abekjohnson17-ui/Ball-Launcher/src/STL Files/MAE476 PROJECT V2/ASSYV2.SLDASM

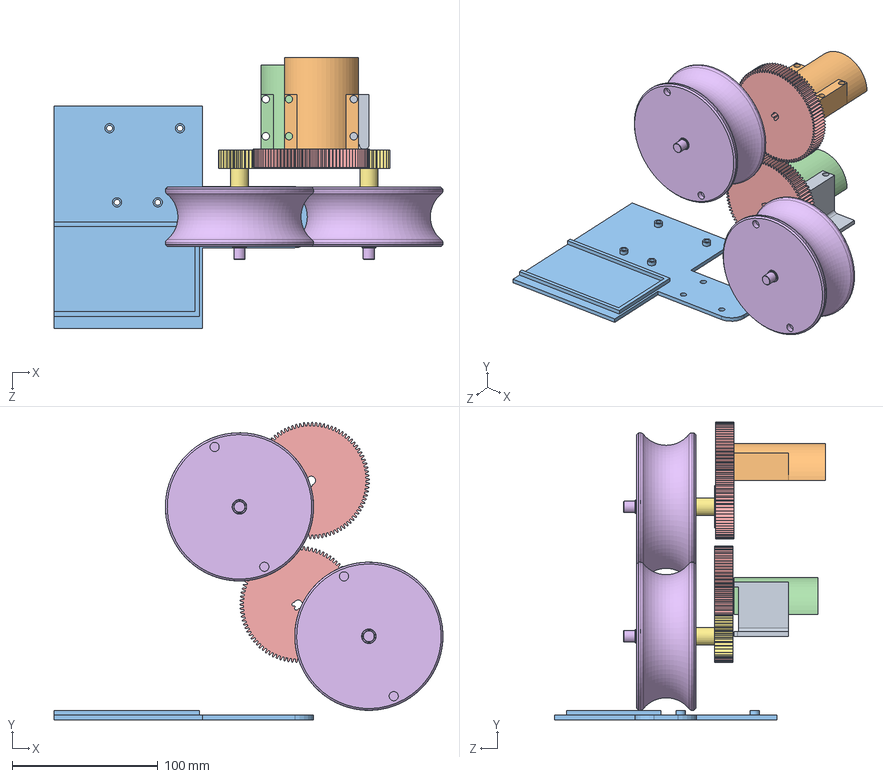
[picture p1: CAD file, 2025-12-07]
src/STL Files/MAE476 PROJECT V2/ASSYV2.SLDASM
266.6 x 204.0 x 185.6 mm
SHAFT-V2 x 2
DRIVENWHEEL x 2
GEARBOTTOM x 2
12VMOUNT
ELECTRONICS
12VMOUNT2
GEARHOLDER
