abekjohnson17-ui/Ball-Launcher/src/STL Files/MAE476 PROJECT V2/ASSY.SLDASM

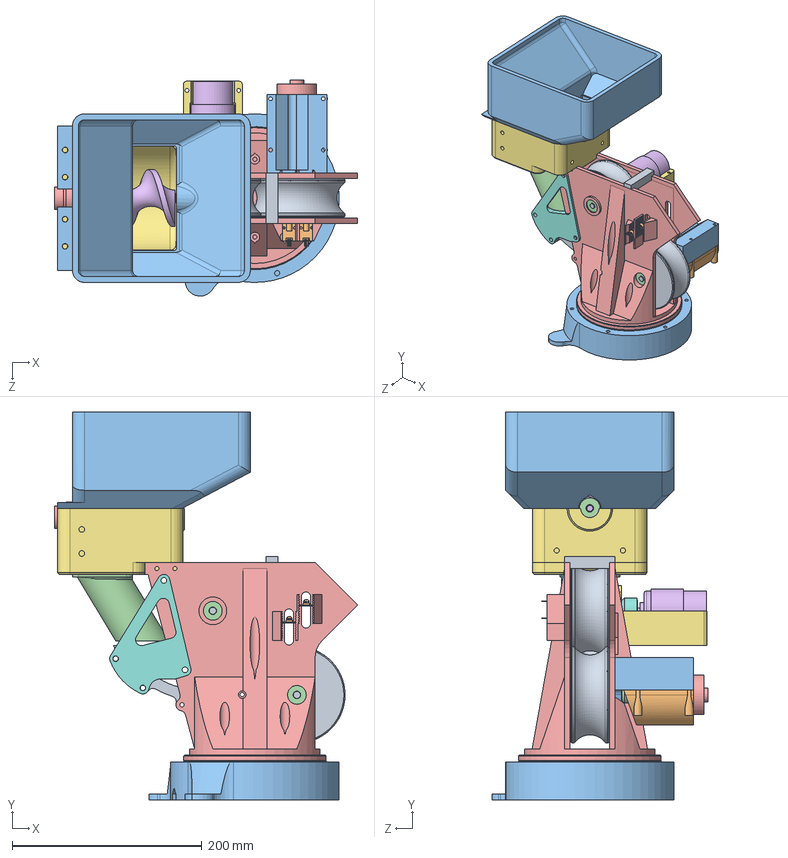
[picture p2: CAD file, 2025-12-07]
src/STL Files/MAE476 PROJECT V2/ASSY.SLDASM
319.9 x 409.2 x 228.0 mm
TESTTURRET
BEARING x 3
BASE
SERVO x 2
TRACK
TRACKARMS
AUGERTRAY
AUGER
MOTOR5V
CHUTE
BUCKET
LAZEREMITTER x 2
DRIVENWHEEL x 2
SHAFT
MOTORMOUNT2
MOTOR36V
MOTOR2
SHAFT2
MOTORMOUNT3
MOTORBRACKET3
SPREADER
