abekjohnson17-ui/Ball-Launcher/src/STL Files/MAE476 Project/MOTORMOUNT2.SLDPRT

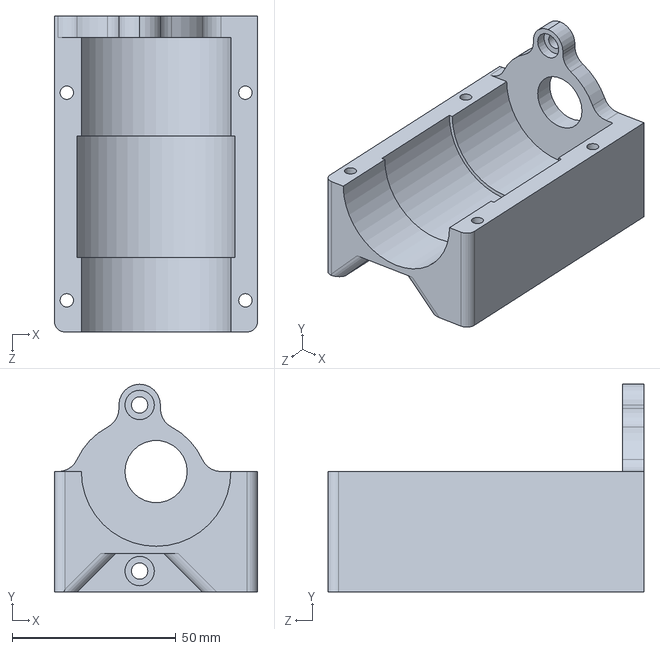
[picture p17: CAD file, 2025-12-07]
src/STL Files/MAE476 Project/MOTORMOUNT2.SLDPRT
62.1 x 63.5 x 96.6 mm
