abekjohnson17-ui/Ball-Launcher/src/STL Files/MAE476 PROJECT V2/TURRETBASE.SLDPRT

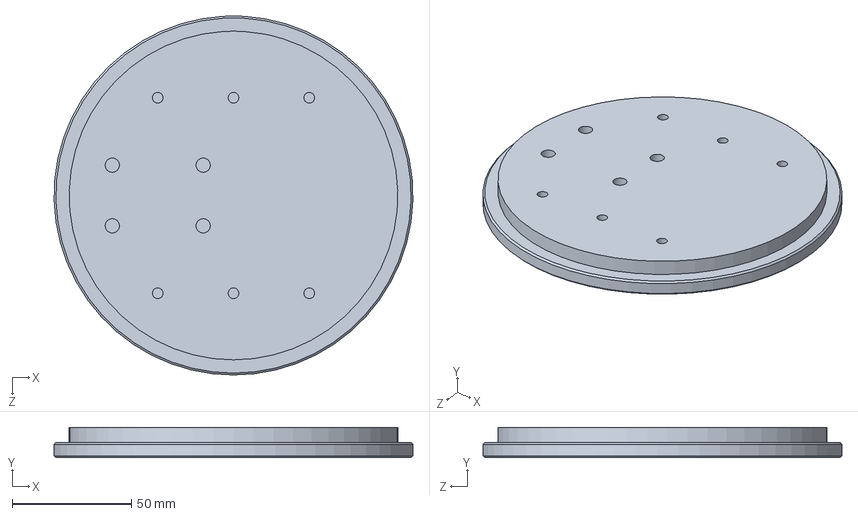
[picture p18: CAD file, 2025-12-07]
src/STL Files/MAE476 PROJECT V2/TURRETBASE.SLDPRT
150.4 x 12.7 x 150.5 mm
