abekjohnson17-ui/Ball-Launcher/src/STL Files/MAE476 Project/SHAFT.SLDPRT

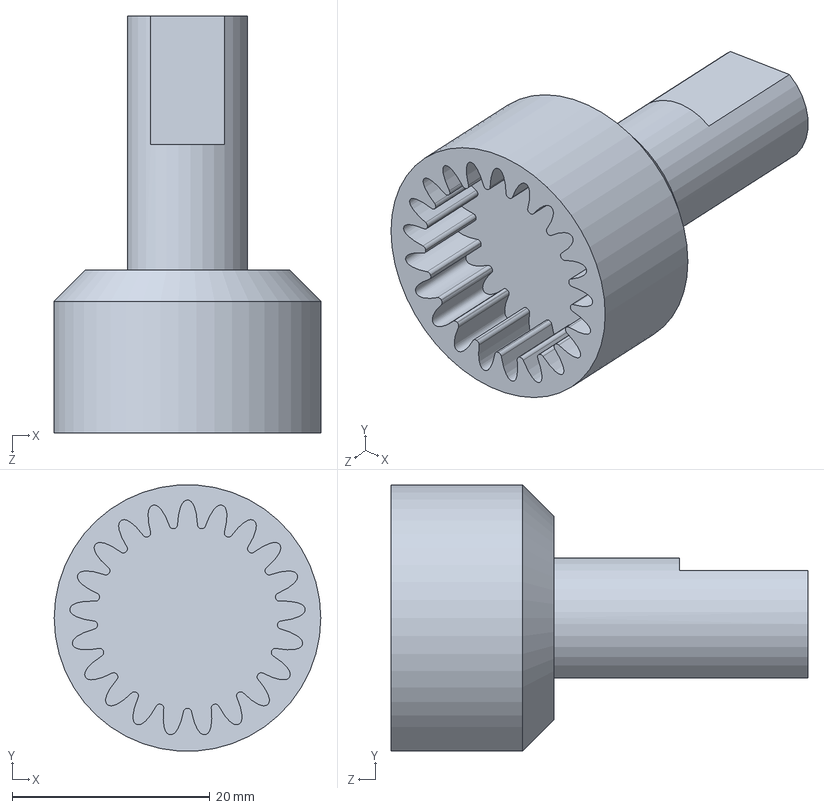
[picture p19: CAD file, 2025-12-07]
src/STL Files/MAE476 Project/SHAFT.SLDPRT
27.0 x 26.9 x 42.2 mm
