abekjohnson17-ui/Ball-Launcher/src/STL Files/MAE476 PROJECT V2/SPREADER.SLDPRT

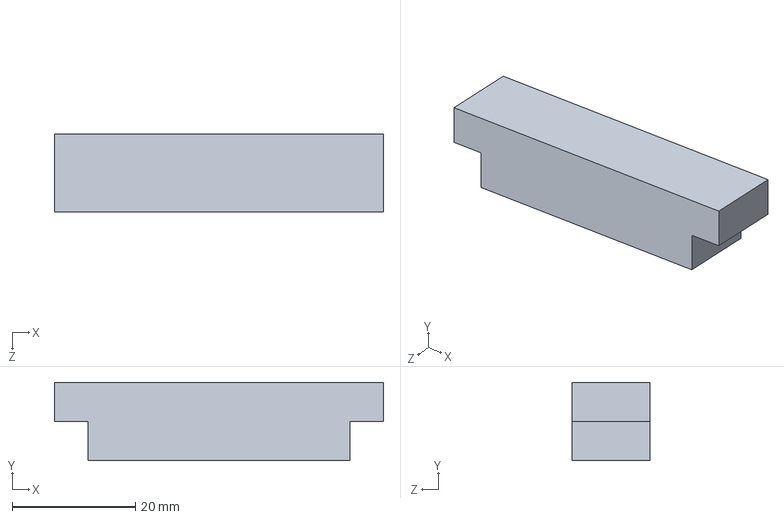
[picture p20: CAD file, 2025-12-07]
src/STL Files/MAE476 PROJECT V2/SPREADER.SLDPRT
53.4 x 12.7 x 12.7 mm
