abekjohnson17-ui/Ball-Launcher/src/STL Files/MAE476 PROJECT V2/SHAFT-V2.SLDPRT

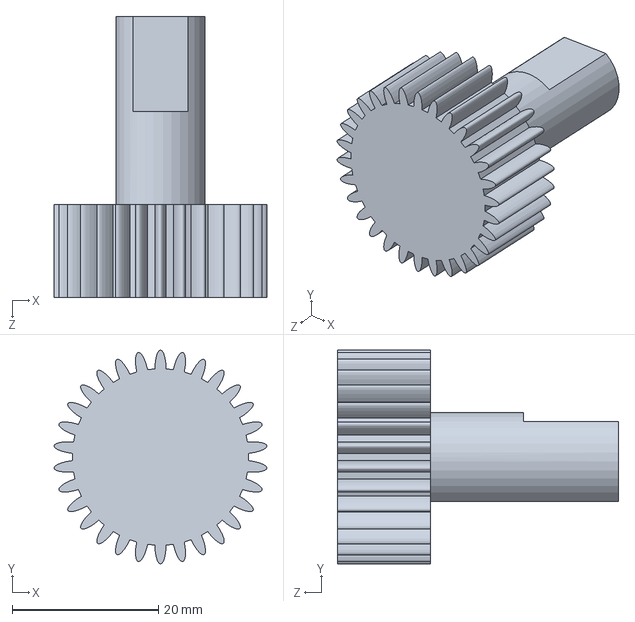
[picture p22: CAD file, 2025-12-07]
src/STL Files/MAE476 PROJECT V2/SHAFT-V2.SLDPRT
29.1 x 29.2 x 38.4 mm
