abekjohnson17-ui/Ball-Launcher/src/STL Files/MAE476 Project/MOTOR2.SLDPRT

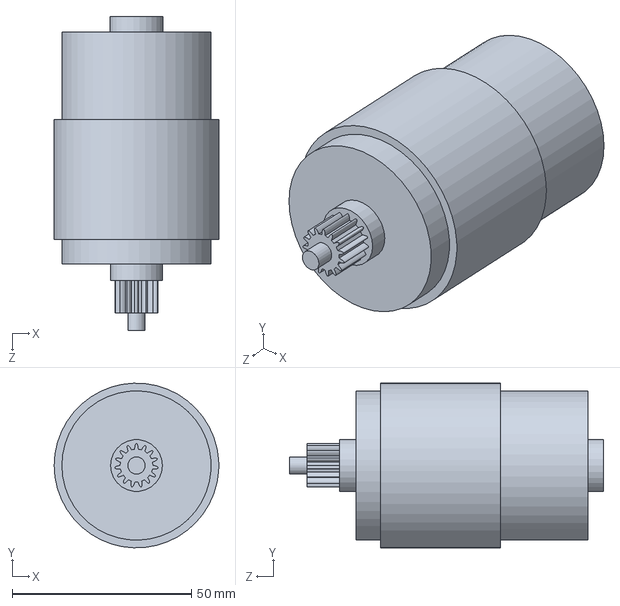
[picture p23: CAD file, 2025-12-07]
src/STL Files/MAE476 Project/MOTOR2.SLDPRT
46.0 x 45.9 x 87.6 mm
