abekjohnson17-ui/Ball-Launcher/src/STL Files/MAE476 Project/MOTORBRACKET3.SLDPRT

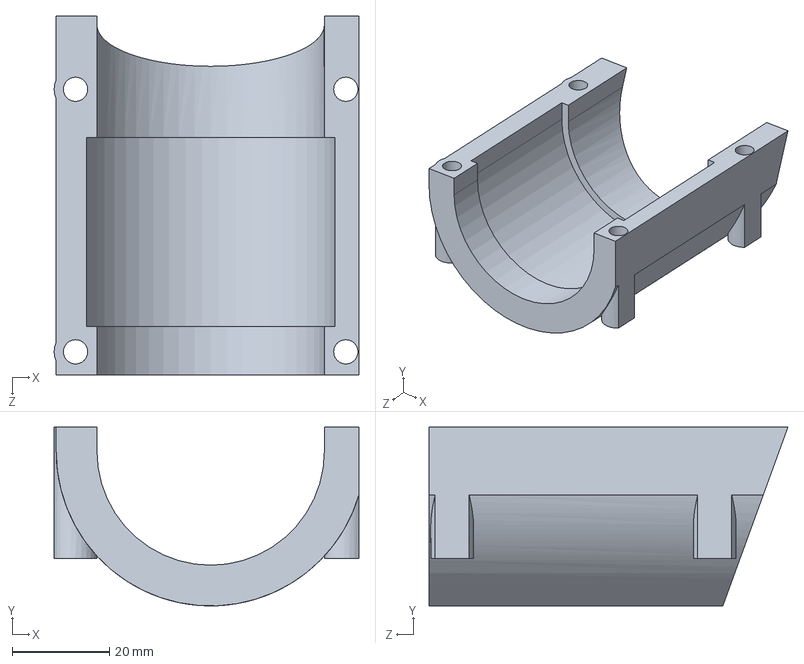
[picture p24: CAD file, 2025-12-07]
src/STL Files/MAE476 Project/MOTORBRACKET3.SLDPRT
62.7 x 36.8 x 73.8 mm
