abekjohnson17-ui/Ball-Launcher/src/STL Files/MAE476 Project/AUGERTRAY.SLDPRT

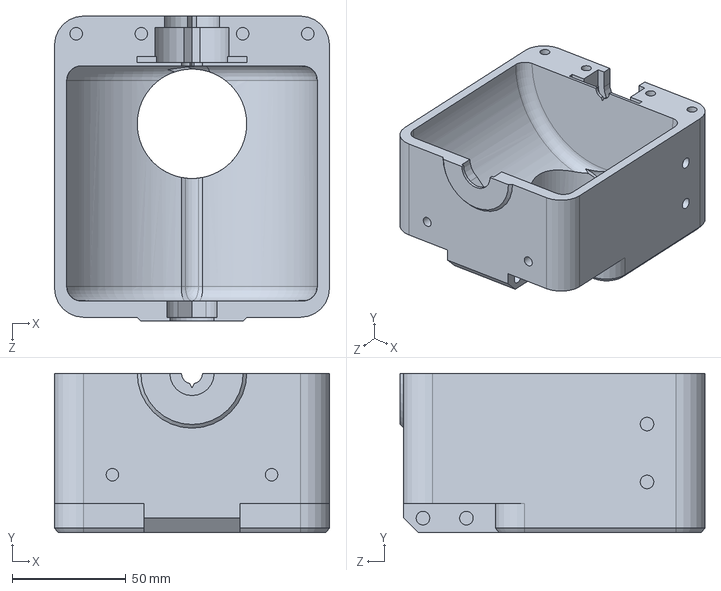
[picture p25: CAD file, 2025-12-07]
src/STL Files/MAE476 Project/AUGERTRAY.SLDPRT
120.7 x 69.8 x 133.7 mm
