abekjohnson17-ui/Ball-Launcher/src/STL Files/MAE476 Project/BUCKET.SLDPRT

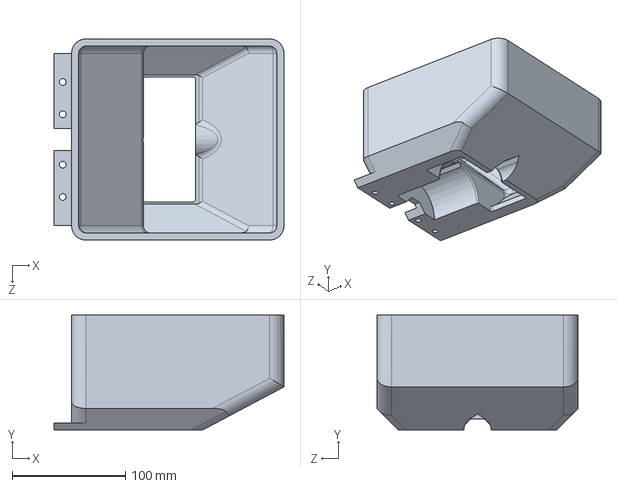
[picture p26: CAD file, 2025-12-07]
src/STL Files/MAE476 Project/BUCKET.SLDPRT
203.2 x 101.6 x 177.8 mm
