abekjohnson17-ui/Ball-Launcher/src/STL Files/MAE476 Project/AUGER.SLDPRT

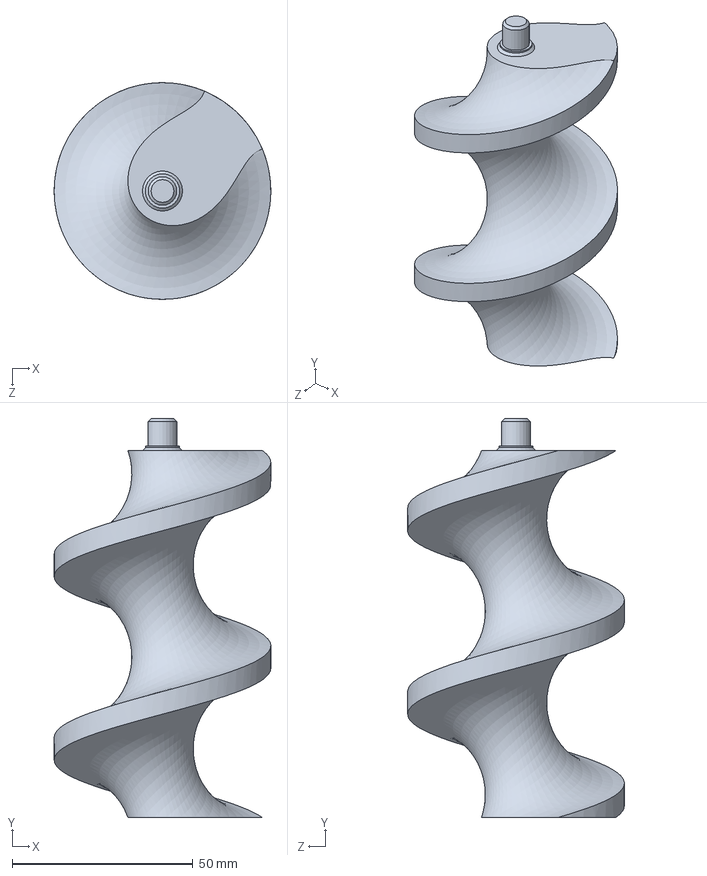
[picture p27: CAD file, 2025-12-07]
src/STL Files/MAE476 Project/AUGER.SLDPRT
60.0 x 110.5 x 60.0 mm
