abekjohnson17-ui/Ball-Launcher/src/STL Files/MAE476 Project/BEARING.SLDPRT

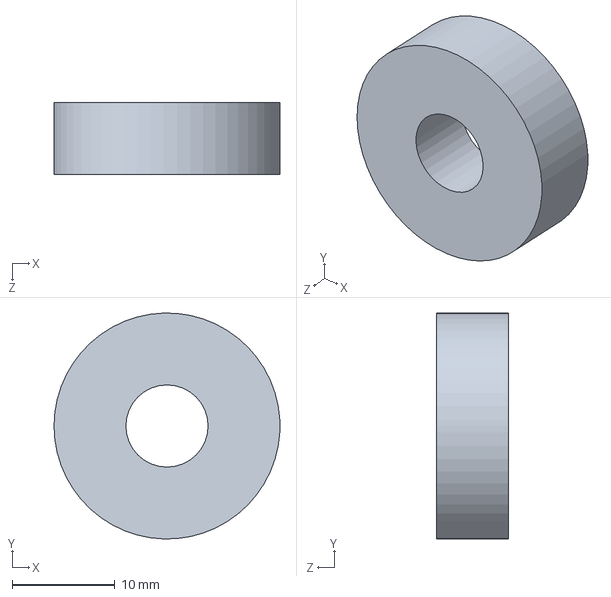
[picture p28: CAD file, 2025-12-07]
src/STL Files/MAE476 Project/BEARING.SLDPRT
22.0 x 22.0 x 7.00 mm
