abekjohnson17-ui/Ball-Launcher/src/STL Files/MAE476 PROJECT V2/MOTOR36V.SLDPRT

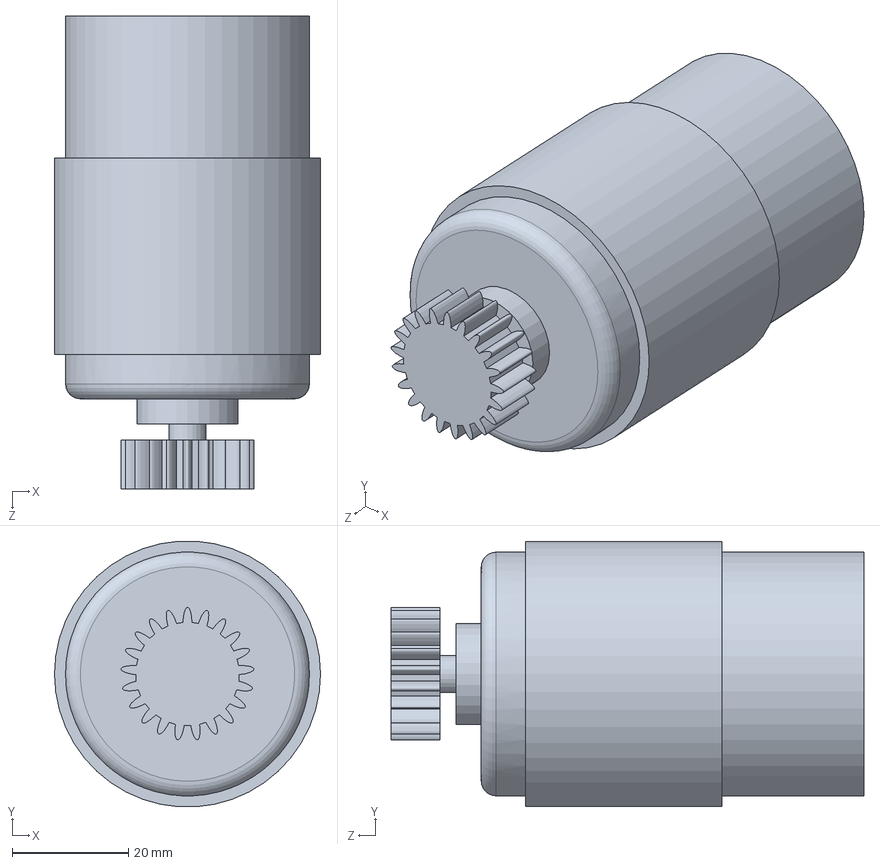
[picture p29: CAD file, 2025-12-07]
src/STL Files/MAE476 PROJECT V2/MOTOR36V.SLDPRT
45.7 x 45.6 x 81.3 mm
