abekjohnson17-ui/Ball-Launcher/src/STL Files/MAE476 Project/SHAFT2.SLDPRT

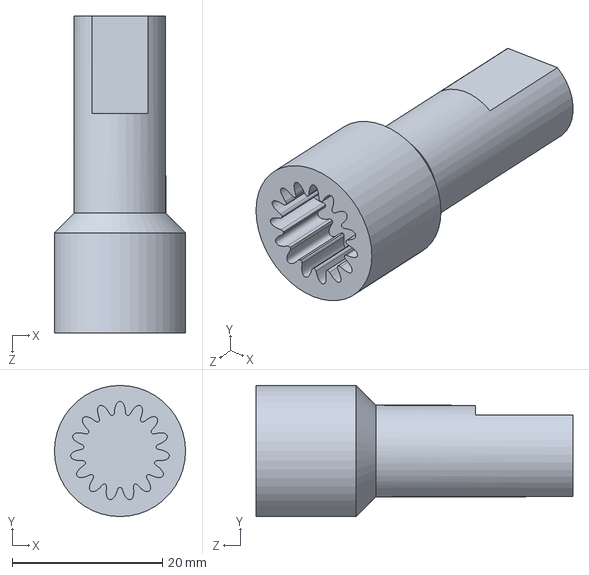
[picture p30: CAD file, 2025-12-07]
src/STL Files/MAE476 Project/SHAFT2.SLDPRT
17.5 x 17.5 x 42.2 mm
