abekjohnson17-ui/Ball-Launcher/src/STL Files/MAE476 PROJECT V2/MOTOR5V.SLDPRT

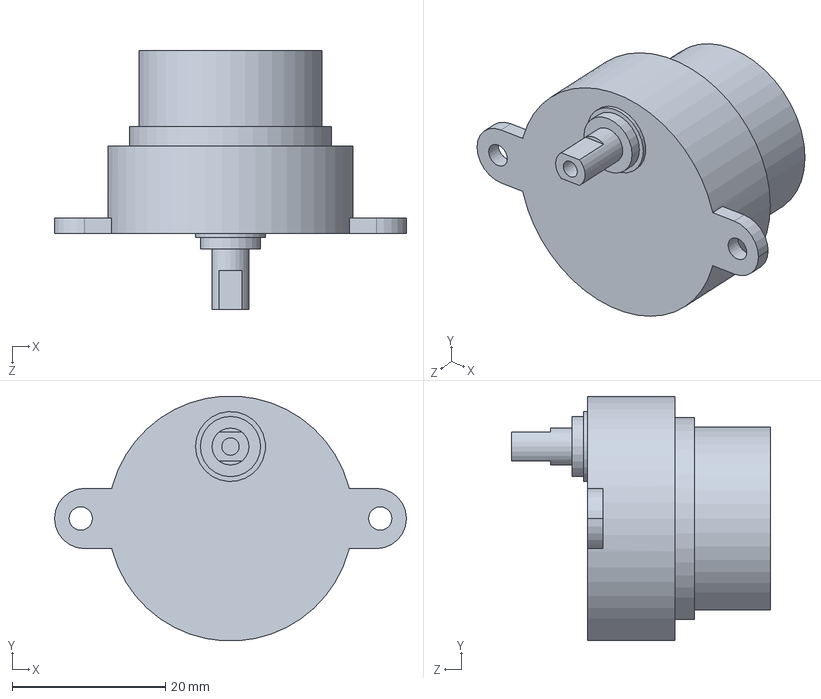
[picture p31: CAD file, 2025-12-07]
src/STL Files/MAE476 PROJECT V2/MOTOR5V.SLDPRT
46.0 x 31.9 x 33.8 mm
