abekjohnson17-ui/Ball-Launcher/src/STL Files/MAE476 Project/TRACK.SLDPRT

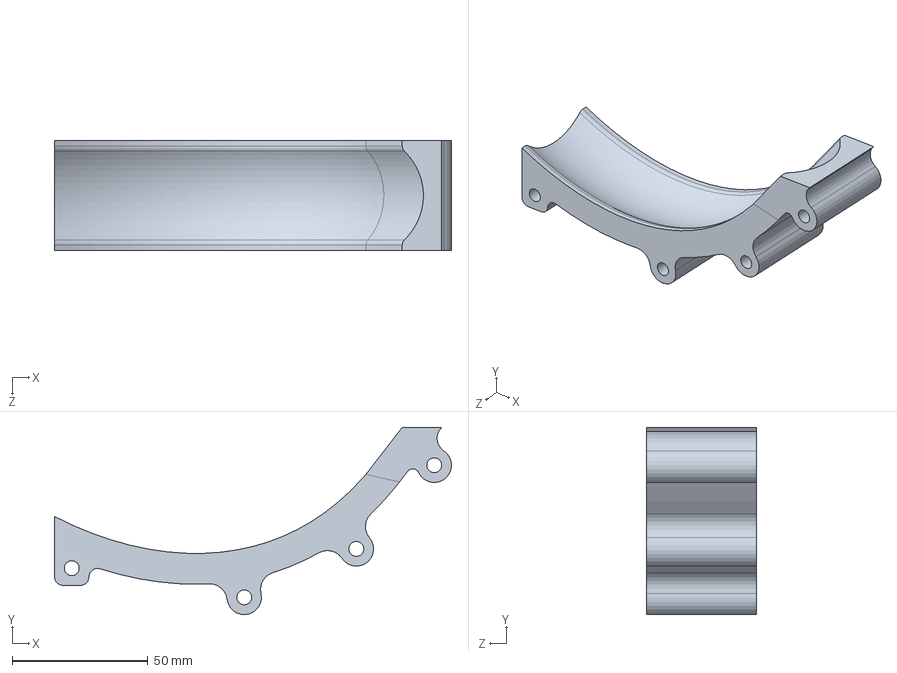
[picture p32: CAD file, 2025-12-07]
src/STL Files/MAE476 Project/TRACK.SLDPRT
146.1 x 68.9 x 40.6 mm
