abekjohnson17-ui/Ball-Launcher/src/STL Files/MAE476 Project/MOTORMOUNT.SLDPRT

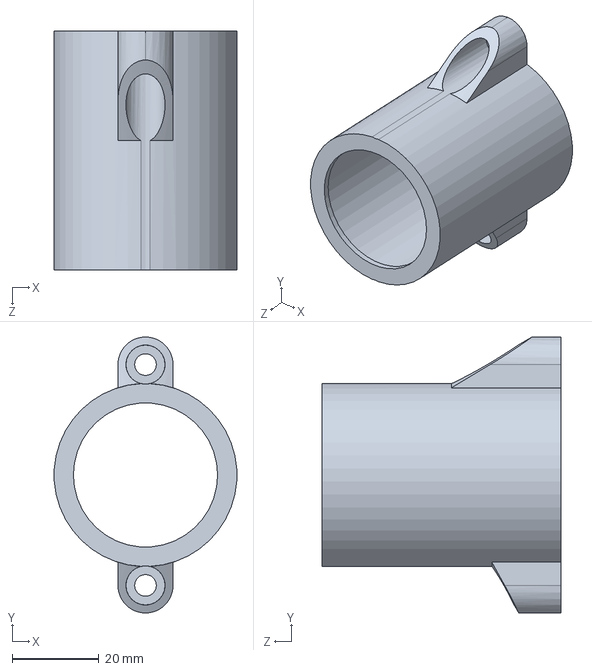
[picture p33: CAD file, 2025-12-07]
src/STL Files/MAE476 Project/MOTORMOUNT.SLDPRT
42.0 x 63.5 x 54.9 mm
