abekjohnson17-ui/Ball-Launcher/src/STL Files/MAE476 Project/TURRETLEFT.SLDPRT

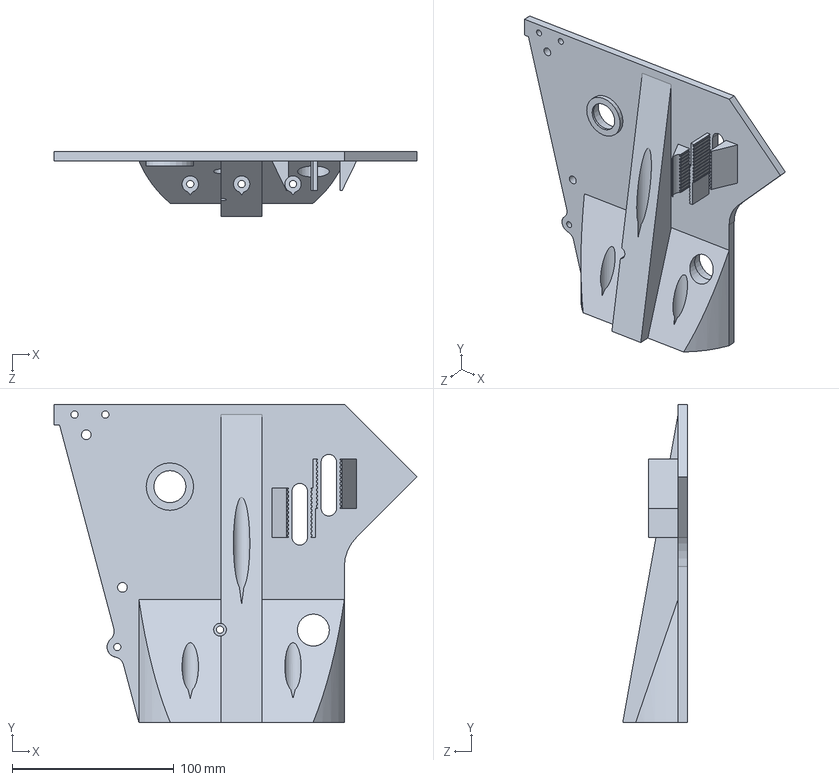
[picture p34: CAD file, 2025-12-07]
src/STL Files/MAE476 Project/TURRETLEFT.SLDPRT
224.4 x 196.9 x 40.0 mm
