abekjohnson17-ui/Ball-Launcher/src/STL Files/MAE476 Project/MOTOR12V.SLDPRT

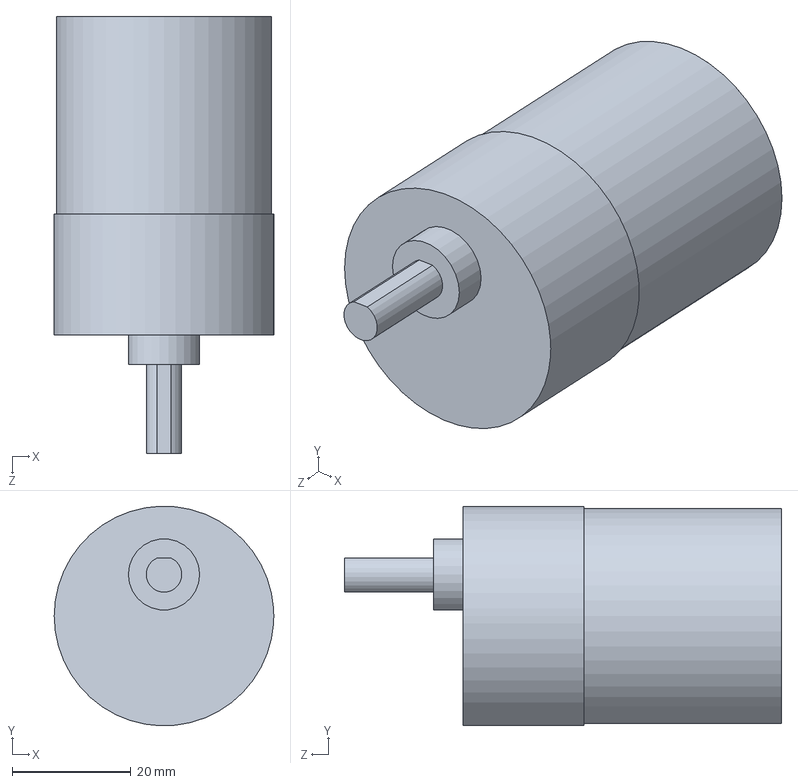
[picture p35: CAD file, 2025-12-07]
src/STL Files/MAE476 Project/MOTOR12V.SLDPRT
37.0 x 37.0 x 73.6 mm
