abekjohnson17-ui/Ball-Launcher/src/STL Files/MAE476 PROJECT V2/MOTORMOUTBOT.SLDPRT

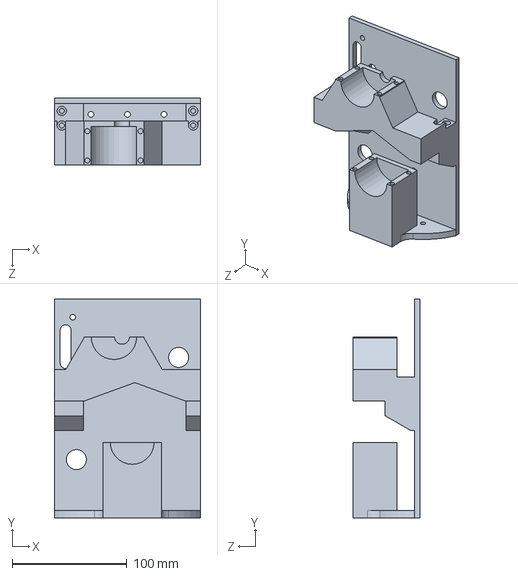
[picture p36: CAD file, 2025-12-07]
src/STL Files/MAE476 PROJECT V2/MOTORMOUTBOT.SLDPRT
127.0 x 190.5 x 58.1 mm
