abekjohnson17-ui/Ball-Launcher/src/STL Files/MAE476 PROJECT V2/shim.SLDPRT

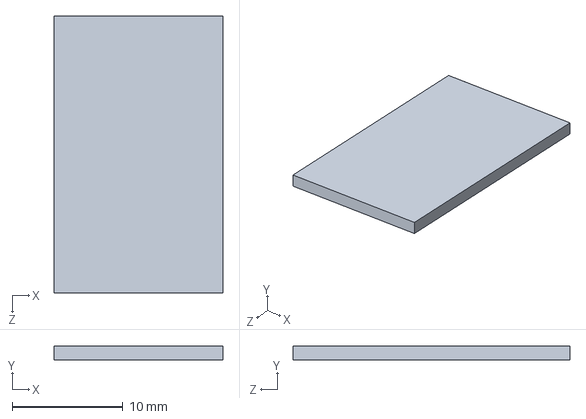
[picture p37: CAD file, 2025-12-07]
src/STL Files/MAE476 PROJECT V2/shim.SLDPRT
15.2 x 1.27 x 25.0 mm
