abekjohnson17-ui/Ball-Launcher/src/STL Files/MAE476 Project/BASETOP.SLDPRT

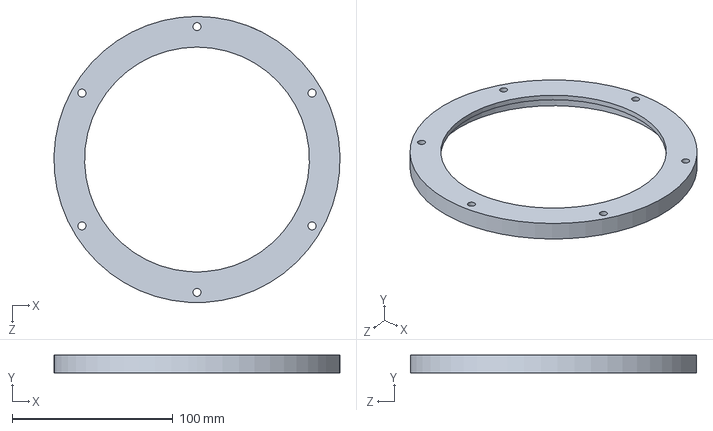
[picture p38: CAD file, 2025-12-07]
src/STL Files/MAE476 Project/BASETOP.SLDPRT
177.7 x 11.1 x 177.8 mm
