abekjohnson17-ui/Ball-Launcher/src/STL Files/MAE476 Project/BALL.SLDPRT

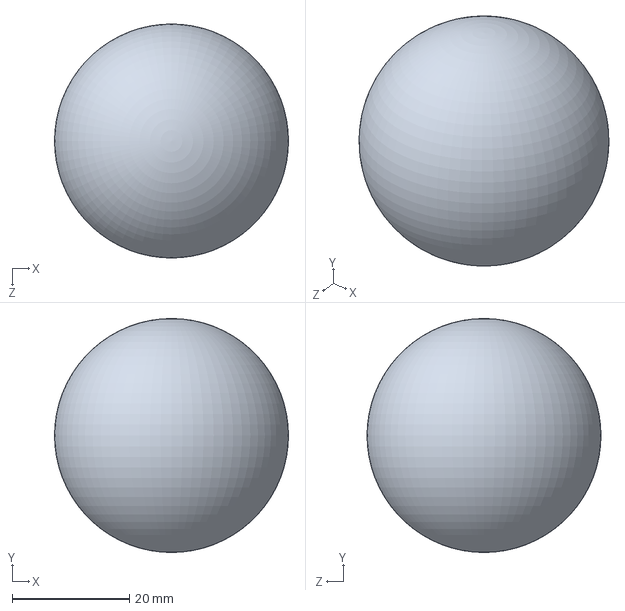
[picture p39: CAD file, 2025-12-07]
src/STL Files/MAE476 Project/BALL.SLDPRT
40.0 x 40.0 x 40.0 mm
