abekjohnson17-ui/Ball-Launcher/src/STL Files/MAE476 PROJECT V2/TESTTURRET-V2.SLDPRT

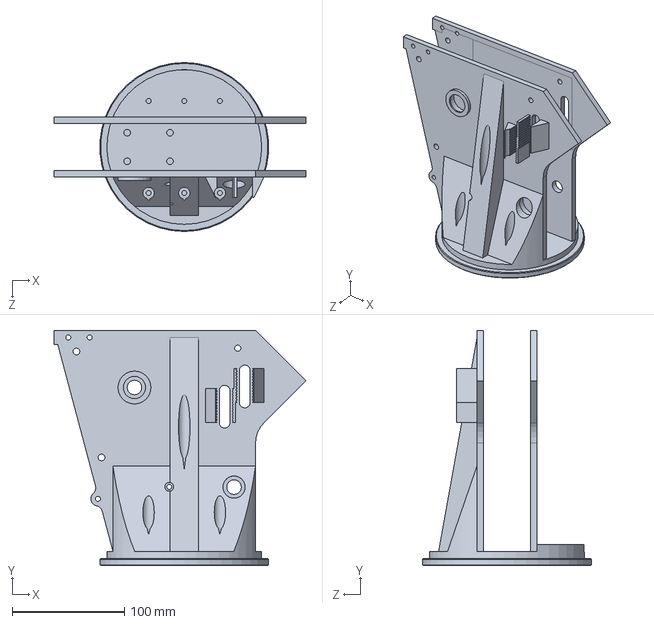
[picture p40: CAD file, 2025-12-07]
src/STL Files/MAE476 PROJECT V2/TESTTURRET-V2.SLDPRT
224.4 x 209.6 x 150.5 mm
