abekjohnson17-ui/Ball-Launcher/src/STL Files/MAE476 Project/LAZERRECEIVER.SLDPRT

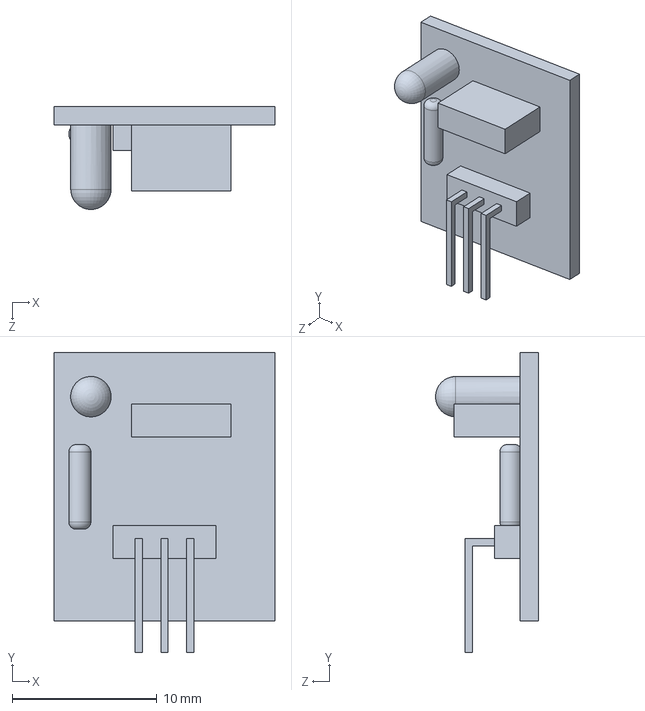
[picture p41: CAD file, 2025-12-07]
src/STL Files/MAE476 Project/LAZERRECEIVER.SLDPRT
15.2 x 20.7 x 7.11 mm
